se1yu/BlockBlast/software/images/Blocks/Home.bmp

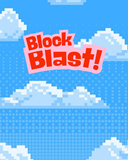
software/images/Blocks/Home.bmp
